hringdrifi/bifrost/outputs/bom_aggregate/aggregate-preview.png

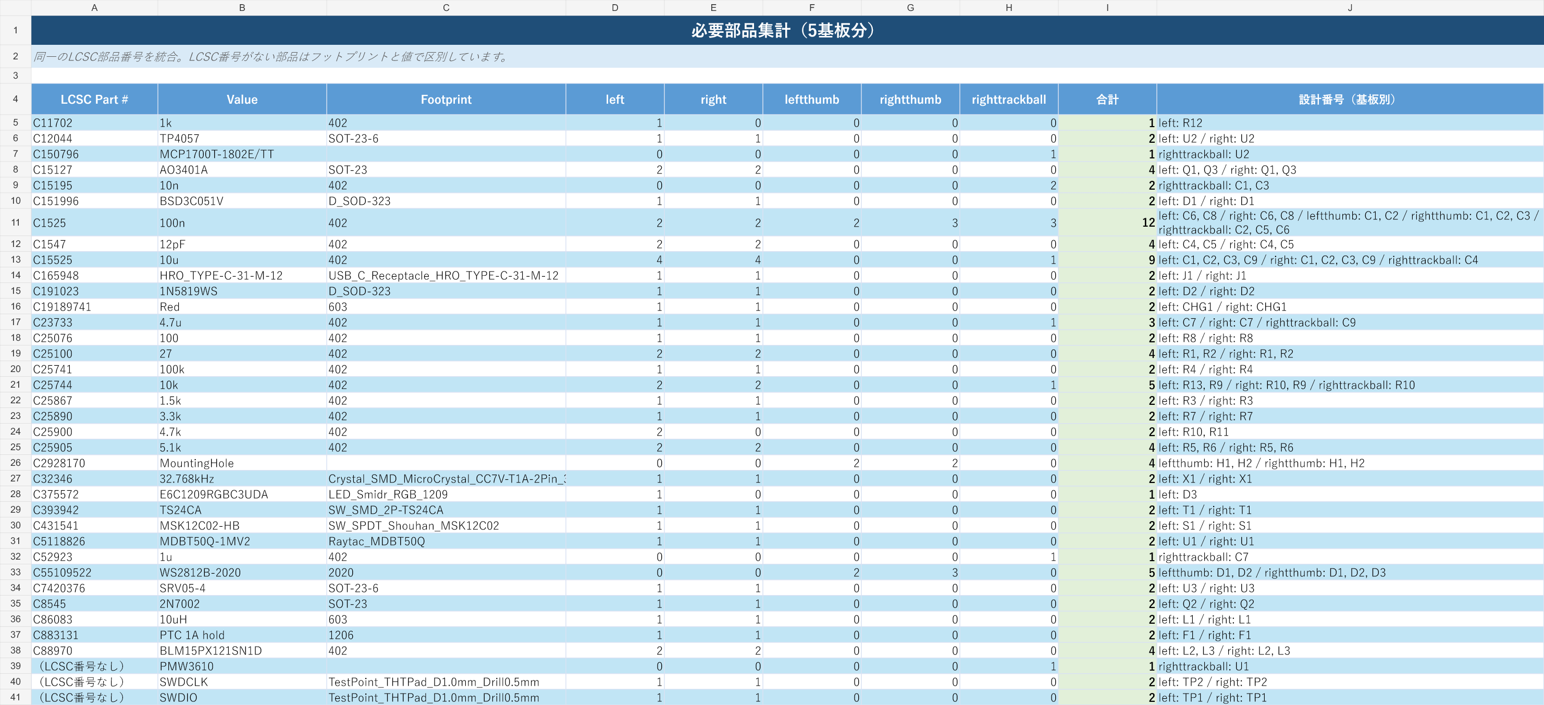
outputs/bom_aggregate/aggregate-preview.png
