hringdrifi/bifrost/outputs/bom_aggregate/before-Sheet1.png

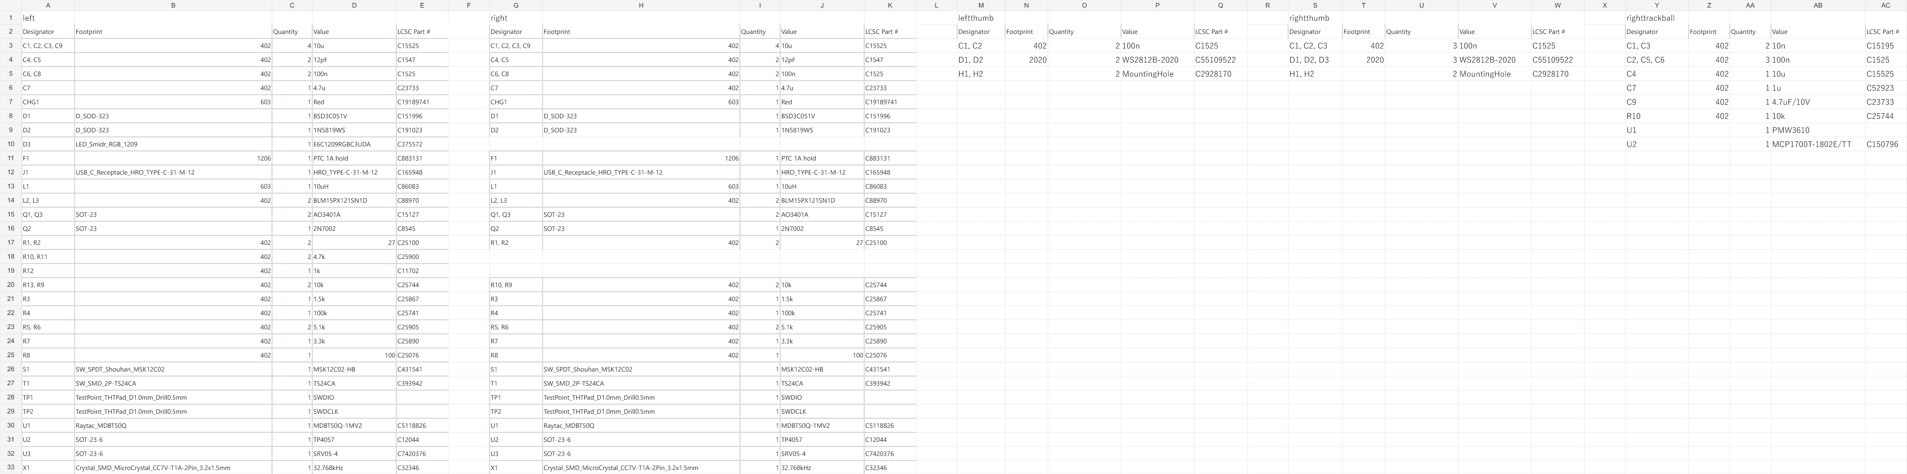
outputs/bom_aggregate/before-Sheet1.png
