hringdrifi/bifrost/case/bifrost_right_thumb_plate.step

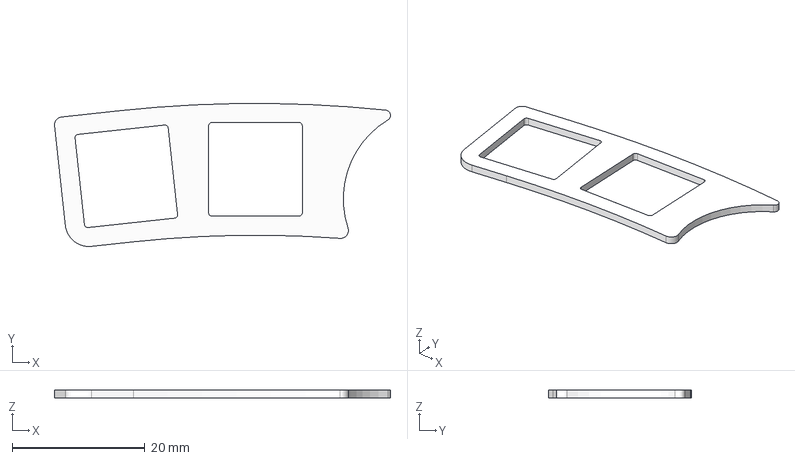
[picture p17: CAD file, 2026-08-18]
case/bifrost_right_thumb_plate.step
50.6 x 21.5 x 1.20 mm
