hringdrifi/bifrost/pcb/left_kicad/3dmodels/Low Profile Keycap 1.25U.step

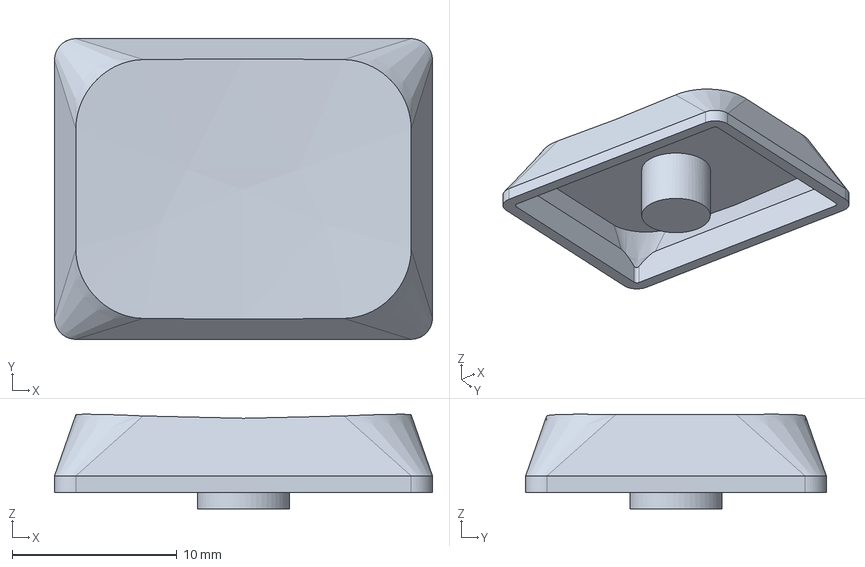
[picture p18: CAD file, 2026-08-13]
pcb/left_kicad/3dmodels/Low Profile Keycap 1.25U.step
22.9 x 18.2 x 5.73 mm
