hringdrifi/bifrost/pcb/right_kicad/3dmodels/Low Profile Keycap 1U.step

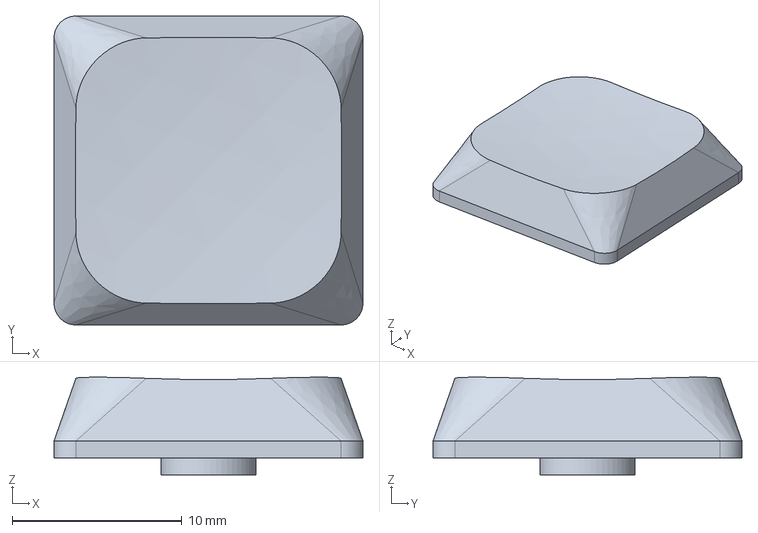
[picture p19: CAD file, 2026-08-13]
pcb/right_kicad/3dmodels/Low Profile Keycap 1U.step
18.2 x 18.2 x 5.76 mm
