hringdrifi/bifrost/case/bifrost_left_thumb_plate.step

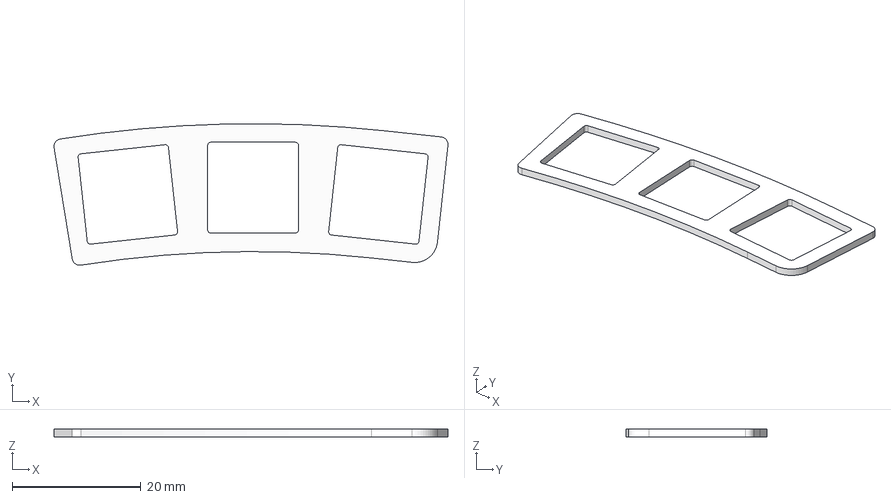
[picture p20: CAD file, 2026-08-18]
case/bifrost_left_thumb_plate.step
61.2 x 22.0 x 1.20 mm
