hringdrifi/bifrost/pcb/left_kicad/3dmodels/Low Profile Keycap 2U.step

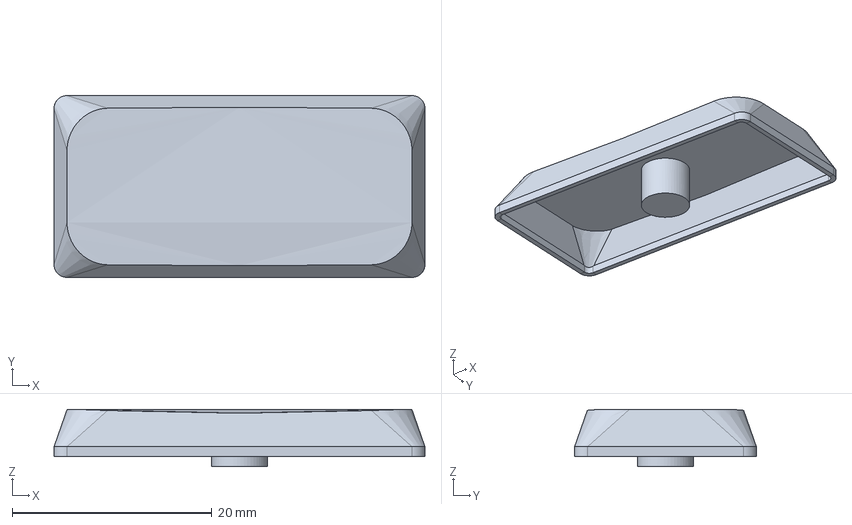
[picture p21: CAD file, 2026-08-13]
pcb/left_kicad/3dmodels/Low Profile Keycap 2U.step
37.2 x 18.2 x 5.75 mm
